voldien/xmas-led-matrix-card/firmware/animation_list.c

#include"animation.h"


const struct rgb_t PROGMEM animations[NRANIM][NRKEYFRAME][NUMROWS * RGBRES] = {

		/*	First animation.	*/
		CREATE_ANIMATION(

			/*	Simple row shift.	*/
			CREATE_RGBK_KEY_FRAME(
				CREATE_RGB_VALUE(31,31,31),		CREATE_RGB_VALUE(31,31,31), CREATE_RGB_VALUE(31,31,31),
				CREATE_RGB_VALUE(0,0,0),		CREATE_RGB_VALUE(0,0,0), 	CREATE_RGB_VALUE(0,0,0),
				CREATE_RGB_VALUE(31,31,31),		CREATE_RGB_VALUE(31,31,31), CREATE_RGB_VALUE(31,31,31),
				CREATE_RGB_VALUE(0,0,0),		CREATE_RGB_VALUE(0,0,0), 	CREATE_RGB_VALUE(0,0,0)),
			CREATE_RGBK_KEY_FRAME(
				CREATE_RGB_VALUE(0,0,0),		CREATE_RGB_VALUE(0,0,0), 	CREATE_RGB_VALUE(0,0,0),
				CREATE_RGB_VALUE(31,31,31),		CREATE_RGB_VALUE(31,31,31), CREATE_RGB_VALUE(31,31,31),
				CREATE_RGB_VALUE(0,0,0),		CREATE_RGB_VALUE(0,0,0), 	CREATE_RGB_VALUE(0,0,0),
				CREATE_RGB_VALUE(31,31,31),		CREATE_RGB_VALUE(31,31,31), CREATE_RGB_VALUE(31,31,31)),

			/*	Simple Column shift.	*/
			CREATE_RGBK_KEY_FRAME(
				CREATE_RGB_VALUE(31,0,0),		CREATE_RGB_VALUE(31,0,0), 	CREATE_RGB_VALUE(31,0,0),
				CREATE_RGB_VALUE(31,0,0),		CREATE_RGB_VALUE(31,0,0), 	CREATE_RGB_VALUE(31,0,0),
				CREATE_RGB_VALUE(31,0,0),		CREATE_RGB_VALUE(31,0,0), 	CREATE_RGB_VALUE(31,0,0),
				CREATE_RGB_VALUE(31,0,0),		CREATE_RGB_VALUE(31,0,0), 	CREATE_RGB_VALUE(31,0,0)),
			CREATE_RGBK_KEY_FRAME(
				CREATE_RGB_VALUE(0,31,0),		CREATE_RGB_VALUE(0,31,0), 	CREATE_RGB_VALUE(0,31,0),
				CREATE_RGB_VALUE(0,31,0),		CREATE_RGB_VALUE(0,31,0), 	CREATE_RGB_VALUE(0,31,0),
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
				CREATE_RGB_VALUE(0,0,0),		CREATE_RGB_VALUE(0,0,0), CREATE_RGB_VALUE(0,0,31),
				CREATE_RGB_VALUE(0,0,0),		CREATE_RGB_VALUE(0,0,0), CREATE_RGB_VALUE(0,0,31),
				CREATE_RGB_VALUE(0,0,0),		CREATE_RGB_VALUE(0,0,0), CREATE_RGB_VALUE(0,0,31)),


			/*	Simple row shifting - spec.	*/
			CREATE_RGBK_KEY_FRAME(
				CREATE_RGB_VALUE(31,31,31),		CREATE_RGB_VALUE(31,31,31), CREATE_RGB_VALUE(31,31,31),
				CREATE_RGB_VALUE(0,0,0),		CREATE_RGB_VALUE(0,0,0), 	CREATE_RGB_VALUE(0,0,0),
				CREATE_RGB_VALUE(0,0,0),		CREATE_RGB_VALUE(0,0,0), 	CREATE_RGB_VALUE(0,0,0),
				CREATE_RGB_VALUE(31,31,31),		CREATE_RGB_VALUE(31,31,31), CREATE_RGB_VALUE(31,31,31)),
			CREATE_RGBK_KEY_FRAME(
				CREATE_RGB_VALUE(0,0,0),		CREATE_RGB_VALUE(0,0,0), 	CREATE_RGB_VALUE(0,0,0),
				CREATE_RGB_VALUE(31,31,31),		CREATE_RGB_VALUE(31,31,31), CREATE_RGB_VALUE(31,31,31),
				CREATE_RGB_VALUE(31,31,31),		CREATE_RGB_VALUE(31,31,31), CREATE_RGB_VALUE(31,31,31),
				CREATE_RGB_VALUE(0,0,0),		CREATE_RGB_VALUE(0,0,0), 	CREATE_RGB_VALUE(0,0,0)),
			CREATE_RGBK_KEY_FRAME(
				CREATE_RGB_VALUE(31,31,31),		CREATE_RGB_VALUE(0,0,31), CREATE_RGB_VALUE(31,31,31),
				CREATE_RGB_VALUE(31,31,31),		CREATE_RGB_VALUE(0,0,31), CREATE_RGB_VALUE(31,31,31),
				CREATE_RGB_VALUE(31,31,31),		CREATE_RGB_VALUE(0,0,31), CREATE_RGB_VALUE(31,31,31),
				CREATE_RGB_VALUE(31,31,31),		CREATE_RGB_VALUE(0,0,31), CREATE_RGB_VALUE(31,31,31)),
			CREATE_RGBK_KEY_FRAME(
				CREATE_RGB_VALUE(0,0,0),		CREATE_RGB_VALUE(0,0,0), 	CREATE_RGB_VALUE(0,0,0),
				CREATE_RGB_VALUE(0,0,0),		CREATE_RGB_VALUE(0,0,0), 	CREATE_RGB_VALUE(0,0,0),
				CREATE_RGB_VALUE(0,0,0),		CREATE_RGB_VALUE(0,0,0), 	CREATE_RGB_VALUE(0,0,0),
				CREATE_RGB_VALUE(0,0,0),		CREATE_RGB_VALUE(0,0,0), 	CREATE_RGB_VALUE(0,0,0))
		),
		/*	Third animation.	*/
		CREATE_ANIMATION(

			/*	Ripple.	*/
			CREATE_RGBK_KEY_FRAME(
				CREATE_RGB_VALUE(0,0,0),		CREATE_RGB_VALUE(0,0,0), 	CREATE_RGB_VALUE(0,0,0),
				CREATE_RGB_VALUE(0,0,0),		CREATE_RGB_VALUE(0,0,0), 	CREATE_RGB_VALUE(0,0,0),
				CREATE_RGB_VALUE(0,0,0),		CREATE_RGB_VALUE(0,0,0), 	CREATE_RGB_VALUE(0,0,0),
				CREATE_RGB_VALUE(0,0,0),		CREATE_RGB_VALUE(0,0,0), 	CREATE_RGB_VALUE(0,0,0)),
			CREATE_RGBK_KEY_FRAME(
				CREATE_RGB_VALUE(0,0,0),		CREATE_RGB_VALUE(0,0,0), 	CREATE_RGB_VALUE(0,0,0),
				CREATE_RGB_VALUE(0,0,0),		CREATE_RGB_VALUE(8,8,0), 	CREATE_RGB_VALUE(0,0,0),
				CREATE_RGB_VALUE(0,0,0),		CREATE_RGB_VALUE(8,8,0), 	CREATE_RGB_VALUE(0,0,0),
				CREATE_RGB_VALUE(0,0,0),		CREATE_RGB_VALUE(0,0,0), 	CREATE_RGB_VALUE(0,0,0)),
			CREATE_RGBK_KEY_FRAME(
				CREATE_RGB_VALUE(0,0,8),		CREATE_RGB_VALUE(8,8,8), 	CREATE_RGB_VALUE(0,0,0),
				CREATE_RGB_VALUE(0,0,8),		CREATE_RGB_VALUE(16,16,8), 	CREATE_RGB_VALUE(0,0,0),
				CREATE_RGB_VALUE(0,0,8),		CREATE_RGB_VALUE(16,16,8), 	CREATE_RGB_VALUE(0,0,0),
				CREATE_RGB_VALUE(0,0,8),		CREATE_RGB_VALUE(8,8,8), 	CREATE_RGB_VALUE(0,0,0)),
			CREATE_RGBK_KEY_FRAME(
				CREATE_RGB_VALUE(0,8,16),		CREATE_RGB_VALUE(16,16,16), 	CREATE_RGB_VALUE(8,0,0),
				CREATE_RGB_VALUE(0,8,16),		CREATE_RGB_VALUE(24,24,16), 	CREATE_RGB_VALUE(8,0,0),
				CREATE_RGB_VALUE(0,8,16),		CREATE_RGB_VALUE(24,24,16), 	CREATE_RGB_VALUE(8,0,0),
				CREATE_RGB_VALUE(0,8,16),		CREATE_RGB_VALUE(16,16,16), 	CREATE_RGB_VALUE(8,0,0)),
			CREATE_RGBK_KEY_FRAME(
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
				CREATE_RGB_VALUE(0,0,31),		CREATE_RGB_VALUE(0,0,31), 		CREATE_RGB_VALUE(0,0,0),
				CREATE_RGB_VALUE(0,31,0),		CREATE_RGB_VALUE(0,0,0), 		CREATE_RGB_VALUE(31,0,0),
				CREATE_RGB_VALUE(31,0,0),		CREATE_RGB_VALUE(0,0,0), 		CREATE_RGB_VALUE(0,31,0)),

			CREATE_RGBK_KEY_FRAME(
				CREATE_RGB_VALUE(0,0,0),		CREATE_RGB_VALUE(31,31,0), 			CREATE_RGB_VALUE(0,0,0),
				CREATE_RGB_VALUE(0,0,31),		CREATE_RGB_VALUE(16,16,31), 		CREATE_RGB_VALUE(0,0,0),
				CREATE_RGB_VALUE(0,31,16),		CREATE_RGB_VALUE(0,0,16), 			CREATE_RGB_VALUE(31,0,0),
				CREATE_RGB_VALUE(31,16,0),		CREATE_RGB_VALUE(0,0,0), 			CREATE_RGB_VALUE(16,31,0)),
			CREATE_RGBK_KEY_FRAME(
				CREATE_RGB_VALUE(0,0,16),		CREATE_RGB_VALUE(31,31,16), 		CREATE_RGB_VALUE(0,0,0),
				CREATE_RGB_VALUE(0,16,31),		CREATE_RGB_VALUE(31,31,31), 		CREATE_RGB_VALUE(16,16,0),
				CREATE_RGB_VALUE(16,31,31),		CREATE_RGB_VALUE(16,16,31), 		CREATE_RGB_VALUE(31,16,0),
				CREATE_RGB_VALUE(31,31,16),		CREATE_RGB_VALUE(0,0,16), 			CREATE_RGB_VALUE(31,31,0)),
			CREATE_RGBK_KEY_FRAME(
				CREATE_RGB_VALUE(0,16,31),		CREATE_RGB_VALUE(31,31,31), 		CREATE_RGB_VALUE(16,0,0),
				CREATE_RGB_VALUE(16,31,31),		CREATE_RGB_VALUE(31,31,31), 		CREATE_RGB_VALUE(31,31,0),
				CREATE_RGB_VALUE(31,31,31),		CREATE_RGB_VALUE(31,31,31), 		CREATE_RGB_VALUE(31,31,0),
				CREATE_RGB_VALUE(31,31,31),		CREATE_RGB_VALUE(16,16,31), 		CREATE_RGB_VALUE(31,31,0)),
			CREATE_RGBK_KEY_FRAME(
				CREATE_RGB_VALUE(16,31,31),		CREATE_RGB_VALUE(31,31,31), 		CREATE_RGB_VALUE(31,16,0),
				CREATE_RGB_VALUE(31,31,31),		CREATE_RGB_VALUE(31,31,31), 		CREATE_RGB_VALUE(31,31,0),
				CREATE_RGB_VALUE(31,31,31),		CREATE_RGB_VALUE(31,31,31), 		CREATE_RGB_VALUE(31,31,0),
				CREATE_RGB_VALUE(31,31,31),		CREATE_RGB_VALUE(31,31,31), 		CREATE_RGB_VALUE(31,31,0)),

			/*	Simple door opening.	*/
			CREATE_RGBK_KEY_FRAME(
				CREATE_RGB_VALUE(31,31,31),		CREATE_RGB_VALUE(31,31,31), CREATE_RGB_VALUE(31,31,31),
				CREATE_RGB_VALUE(31,31,31),		CREATE_RGB_VALUE(31,31,31), CREATE_RGB_VALUE(31,31,31),
				CREATE_RGB_VALUE(31,31,31),		CREATE_RGB_VALUE(31,31,31), CREATE_RGB_VALUE(31,31,31),
				CREATE_RGB_VALUE(31,31,31),		CREATE_RGB_VALUE(31,31,31), CREATE_RGB_VALUE(31,31,31)),
			CREATE_RGBK_KEY_FRAME(
				CREATE_RGB_VALUE(31,31,31),		CREATE_RGB_VALUE(0,0,31), CREATE_RGB_VALUE(31,31,31),
				CREATE_RGB_VALUE(31,31,31),		CREATE_RGB_VALUE(0,0,31), CREATE_RGB_VALUE(31,31,31),
				CREATE_RGB_VALUE(31,31,31),		CREATE_RGB_VALUE(0,0,31), CREATE_RGB_VALUE(31,31,31),
				CREATE_RGB_VALUE(31,31,31),		CREATE_RGB_VALUE(0,0,31), CREATE_RGB_VALUE(31,31,31)),
			CREATE_RGBK_KEY_FRAME(
				CREATE_RGB_VALUE(31,31,0),		CREATE_RGB_VALUE(0,0,0), CREATE_RGB_VALUE(31,31,31),
				CREATE_RGB_VALUE(31,31,0),		CREATE_RGB_VALUE(0,0,0), CREATE_RGB_VALUE(31,31,31),
				CREATE_RGB_VALUE(31,31,0),		CREATE_RGB_VALUE(0,0,0), CREATE_RGB_VALUE(31,31,31),
				CREATE_RGB_VALUE(31,31,0),		CREATE_RGB_VALUE(0,0,0), CREATE_RGB_VALUE(31,31,31)),
			CREATE_RGBK_KEY_FRAME(
				CREATE_RGB_VALUE(31,0,0),		CREATE_RGB_VALUE(0,0,0), CREATE_RGB_VALUE(0,31,31),
				CREATE_RGB_VALUE(31,0,0),		CREATE_RGB_VALUE(0,0,0), CREATE_RGB_VALUE(0,31,31),
				CREATE_RGB_VALUE(31,0,0),		CREATE_RGB_VALUE(0,0,0), CREATE_RGB_VALUE(0,31,31),
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
				CREATE_RGB_VALUE(0,0,0),		CREATE_RGB_VALUE(0,0,8), 		CREATE_RGB_VALUE(16,24,0),
				CREATE_RGB_VALUE(8,16,24),		CREATE_RGB_VALUE(31,0,0), 		CREATE_RGB_VALUE(0,0,0)),
			CREATE_RGBK_KEY_FRAME(
				CREATE_RGB_VALUE(16,24,31),		CREATE_RGB_VALUE(0,0,0), 		CREATE_RGB_VALUE(0,0,0),
				CREATE_RGB_VALUE(0,0,0),		CREATE_RGB_VALUE(8,16,24), 		CREATE_RGB_VALUE(31,0,0),
				CREATE_RGB_VALUE(31,0,0),		CREATE_RGB_VALUE(0,0,0), 		CREATE_RGB_VALUE(8,16,0),
				CREATE_RGB_VALUE(0,8,16),		CREATE_RGB_VALUE(24,31,0), 		CREATE_RGB_VALUE(0,0,0)),
			CREATE_RGBK_KEY_FRAME(
				CREATE_RGB_VALUE(8,16,24),		CREATE_RGB_VALUE(31,0,0), 		CREATE_RGB_VALUE(0,0,0),
				CREATE_RGB_VALUE(0,0,0),		CREATE_RGB_VALUE(0,8,16), 		CREATE_RGB_VALUE(24,31,0),
				CREATE_RGB_VALUE(24,31,0),		CREATE_RGB_VALUE(0,0,0), 		CREATE_RGB_VALUE(0,8,0),
				CREATE_RGB_VALUE(0,0,8),		CREATE_RGB_VALUE(16,24,31), 	CREATE_RGB_VALUE(0,0,0)),
			CREATE_RGBK_KEY_FRAME(
				CREATE_RGB_VALUE(0,8,16),		CREATE_RGB_VALUE(24,31,0), 		CREATE_RGB_VALUE(0,0,0),
				CREATE_RGB_VALUE(0,0,0),		CREATE_RGB_VALUE(0,0,8), 		CREATE_RGB_VALUE(16,24,0),
				CREATE_RGB_VALUE(16,24,31),		CREATE_RGB_VALUE(0,0,0), 		CREATE_RGB_VALUE(0,0,0),
				CREATE_RGB_VALUE(0,0,0),		CREATE_RGB_VALUE(8,16,24), 		CREATE_RGB_VALUE(31,0,0)),
			CREATE_RGBK_KEY_FRAME(
				CREATE_RGB_VALUE(0,0,8),		CREATE_RGB_VALUE(16,24,31), 		CREATE_RGB_VALUE(0,0,0),
				CREATE_RGB_VALUE(0,0,0),		CREATE_RGB_VALUE(0,0,0), 		CREATE_RGB_VALUE(8,16,0),
				CREATE_RGB_VALUE(8,16,24),		CREATE_RGB_VALUE(0,0,0), 		CREATE_RGB_VALUE(0,0,0),
				CREATE_RGB_VALUE(0,0,0),		CREATE_RGB_VALUE(0,8,16), 		CREATE_RGB_VALUE(24,31,0))
		),

};
