voldien/xmas-led-matrix-card/firmware/rgb.h

//
// Copyright (c) 2013 Danny Havenith
//
// Distributed under the Boost Software License, Version 1.0. (See accompanying
// file LICENSE_1_0.txt or copy at http://www.boost.org/LICENSE_1_0.txt)
//


#ifndef RGB_H_
#define RGB_H_
#include<stdio.h>

//namespace ws2811 {





#endif /* RGB_H_ */
